sslivins/thermux/main/wifi_manager.c

/**
 * @file wifi_manager.c
 * @brief WiFi connection management (fallback for when Ethernet unavailable)
 */

#include "wifi_manager.h"
#include "nvs_storage.h"
#include "esp_log.h"
#include "esp_wifi.h"
#include "esp_event.h"
#include "freertos/FreeRTOS.h"
#include "freertos/event_groups.h"
#include <string.h>

static const char *TAG = "wifi_manager";

#define WIFI_MAXIMUM_RETRY  5

static esp_netif_t *s_wifi_netif = NULL;
static bool s_connected = false;
static bool s_scanning = false;  /* Flag to prevent auto-connect during scan */
static char s_ip_addr[16] = {0};
static int s_retry_num = 0;
static EventGroupHandle_t s_wifi_event_group;
static bool s_driver_ready = false;  /* esp_wifi_init() done, netif created */
static bool s_started = false;       /* started by wifi_manager_start() */
static esp_event_handler_instance_t s_wifi_evt_inst;
static esp_event_handler_instance_t s_ip_evt_inst;

#define WIFI_CONNECTED_BIT BIT0
#define WIFI_FAIL_BIT      BIT1

static void wifi_event_handler(void *arg, esp_event_base_t event_base,
                               int32_t event_id, void *event_data)
{
    if (event_base == WIFI_EVENT && event_id == WIFI_EVENT_STA_START) {
        if (!s_scanning) {
            esp_wifi_connect();
        }
    } else if (event_base == WIFI_EVENT && event_id == WIFI_EVENT_STA_DISCONNECTED) {
        if (!s_scanning && s_retry_num < WIFI_MAXIMUM_RETRY) {
            esp_wifi_connect();
            s_retry_num++;
            ESP_LOGD(TAG, "Retry to connect to the AP (%d/%d)", s_retry_num, WIFI_MAXIMUM_RETRY);
        } else if (!s_scanning) {
            xEventGroupSetBits(s_wifi_event_group, WIFI_FAIL_BIT);
            ESP_LOGI(TAG, "Connect to the AP fail");
        }
        s_connected = false;
    } else if (event_base == IP_EVENT && event_id == IP_EVENT_STA_GOT_IP) {
        ip_event_got_ip_t *event = (ip_event_got_ip_t *)event_data;
        snprintf(s_ip_addr, sizeof(s_ip_addr), IPSTR, IP2STR(&event->ip_info.ip));
        ESP_LOGI(TAG, "Got IP: %s", s_ip_addr);
        s_retry_num = 0;
        s_connected = true;
        xEventGroupSetBits(s_wifi_event_group, WIFI_CONNECTED_BIT);
    }
}

/*
 * The WiFi driver is brought up on first use rather than at boot. On an
 * Ethernet unit nothing starts WiFi; it is only used for the settings page's
 * network scan. An initialised but idle driver still held ~20 KB of heap
 * (static RX buffers and driver state), and that is the margin the OTA
 * download's TLS session needs on a busy unit.
 */
esp_err_t wifi_manager_init(void)
{
    s_wifi_event_group = xEventGroupCreate();
    return s_wifi_event_group ? ESP_OK : ESP_ERR_NO_MEM;
}

static void driver_down(void)
{
    if (!s_driver_ready) {
        return;
    }
    esp_event_handler_instance_unregister(WIFI_EVENT, ESP_EVENT_ANY_ID, s_wifi_evt_inst);
    esp_event_handler_instance_unregister(IP_EVENT, IP_EVENT_STA_GOT_IP, s_ip_evt_inst);
    esp_wifi_deinit();
    esp_netif_destroy_default_wifi(s_wifi_netif);
    s_wifi_netif = NULL;
    s_driver_ready = false;
    ESP_LOGD(TAG, "WiFi driver released");
}

static esp_err_t driver_up(void)
{
    if (s_driver_ready) {
        return ESP_OK;
    }
    ESP_LOGD(TAG, "Initializing WiFi");

    s_wifi_netif = esp_netif_create_default_wifi_sta();
    if (s_wifi_netif == NULL) {
        return ESP_ERR_NO_MEM;
    }
    esp_netif_set_hostname(s_wifi_netif, CONFIG_MDNS_HOSTNAME);

    wifi_init_config_t cfg = WIFI_INIT_CONFIG_DEFAULT();
    esp_err_t err = esp_wifi_init(&cfg);
    if (err != ESP_OK) {
        ESP_LOGE(TAG, "esp_wifi_init failed: %s", esp_err_to_name(err));
        esp_netif_destroy_default_wifi(s_wifi_netif);
        s_wifi_netif = NULL;
        return err;
    }
    s_driver_ready = true;

    err = esp_event_handler_instance_register(WIFI_EVENT, ESP_EVENT_ANY_ID,
                                              &wifi_event_handler, NULL, &s_wifi_evt_inst);
    if (err == ESP_OK) {
        err = esp_event_handler_instance_register(IP_EVENT, IP_EVENT_STA_GOT_IP,
                                                  &wifi_event_handler, NULL, &s_ip_evt_inst);
    }

    /* Try to load saved credentials, otherwise use menuconfig defaults */
    char ssid[32] = {0};
    char password[64] = {0};
    if (nvs_storage_load_wifi_config(ssid, sizeof(ssid), password, sizeof(password)) != ESP_OK ||
        strlen(ssid) == 0) {
        strncpy(ssid, CONFIG_WIFI_SSID, sizeof(ssid) - 1);
        strncpy(password, CONFIG_WIFI_PASSWORD, sizeof(password) - 1);
    }

    wifi_config_t wifi_config = {
        .sta = {
            .threshold.authmode = WIFI_AUTH_WPA2_PSK,
            .sae_pwe_h2e = WPA3_SAE_PWE_BOTH,
        },
    };
    strncpy((char *)wifi_config.sta.ssid, ssid, sizeof(wifi_config.sta.ssid) - 1);
    strncpy((char *)wifi_config.sta.password, password, sizeof(wifi_config.sta.password) - 1);

    if (err == ESP_OK) {
        err = esp_wifi_set_mode(WIFI_MODE_STA);
    }
    if (err == ESP_OK) {
        err = esp_wifi_set_config(WIFI_IF_STA, &wifi_config);
    }
    if (err != ESP_OK) {
        ESP_LOGE(TAG, "WiFi setup failed: %s", esp_err_to_name(err));
        driver_down();
        return err;
    }

    ESP_LOGD(TAG, "WiFi initialization complete");
    return ESP_OK;
}

esp_err_t wifi_manager_start(void)
{
    ESP_LOGD(TAG, "Starting WiFi");
    esp_err_t err = driver_up();
    if (err != ESP_OK) {
        return err;
    }
    s_retry_num = 0;
    err = esp_wifi_start();
    if (err == ESP_OK) {
        s_started = true;
    }
    return err;
}

esp_err_t wifi_manager_stop(void)
{
    if (!s_driver_ready) {
        return ESP_OK;
    }
    s_started = false;
    return esp_wifi_stop();
}

bool wifi_manager_is_connected(void)
{
    return s_connected;
}

const char* wifi_manager_get_ip(void)
{
    return s_ip_addr;
}

esp_err_t wifi_manager_set_credentials(const char *ssid, const char *password)
{
    /* Save to NVS */
    esp_err_t err = nvs_storage_save_wifi_config(ssid, password);
    if (err != ESP_OK) {
        return err;
    }

    /* Update running config */
    wifi_config_t wifi_config = {
        .sta = {
            .threshold.authmode = WIFI_AUTH_WPA2_PSK,
        },
    };
    strncpy((char *)wifi_config.sta.ssid, ssid, sizeof(wifi_config.sta.ssid) - 1);
    strncpy((char *)wifi_config.sta.password, password, sizeof(wifi_config.sta.password) - 1);

    /* Not initialised yet: driver_up() reads the saved credentials */
    if (s_driver_ready) {
        esp_wifi_set_config(WIFI_IF_STA, &wifi_config);
    }

    ESP_LOGI(TAG, "WiFi credentials updated");
    return ESP_OK;
}

esp_err_t wifi_manager_scan(wifi_ap_record_t *ap_records, uint16_t max_records, uint16_t *found_count)
{
    ESP_LOGD(TAG, "Starting WiFi scan...");

    /* Set scanning flag to prevent auto-connect in event handler */
    s_scanning = true;

    /* Bring the driver up (and start it) just for the scan if WiFi isn't in
     * use, and give the memory back afterwards. */
    bool brought_up = !s_driver_ready;
    esp_err_t err = driver_up();
    if (err != ESP_OK) {
        s_scanning = false;
        return err;
    }
    bool started_here = !s_started;
    if (started_here) {
        err = esp_wifi_start();
        if (err != ESP_OK) {
            ESP_LOGE(TAG, "WiFi start for scan failed: %s", esp_err_to_name(err));
            goto done;
        }
        ESP_LOGD(TAG, "WiFi started temporarily for scan");
    }

    vTaskDelay(pdMS_TO_TICKS(100)); /* Brief delay for WiFi to stabilize */

    wifi_scan_config_t scan_config = {
        .ssid = NULL,
        .bssid = NULL,
        .channel = 0,
        .show_hidden = false,
        .scan_type = WIFI_SCAN_TYPE_ACTIVE,
        .scan_time.active.min = 100,
        .scan_time.active.max = 300,
    };

    /* Start blocking scan */
    err = esp_wifi_scan_start(&scan_config, true);
    if (err != ESP_OK) {
        ESP_LOGE(TAG, "WiFi scan failed to start: %s", esp_err_to_name(err));
        goto done;
    }

    uint16_t ap_count = 0;
    esp_wifi_scan_get_ap_num(&ap_count);
    ESP_LOGD(TAG, "WiFi scan found %d networks", ap_count);
    if (ap_count > max_records) {
        ap_count = max_records;
    }

    err = esp_wifi_scan_get_ap_records(&ap_count, ap_records);
    if (err != ESP_OK) {
        ESP_LOGE(TAG, "Failed to get scan results: %s", esp_err_to_name(err));
        goto done;
    }
    *found_count = ap_count;

done:
    if (started_here) {
        esp_wifi_stop();
        ESP_LOGD(TAG, "WiFi stopped after scan");
    }
    if (brought_up) {
        driver_down();
    }
    s_scanning = false;
    return err;
}
